CalPlug/Thrmostat_2_HVAC_IR_Controller/firmware/MQTT/AP.h

/**********************************
* CalPlug Portable AC Integration
* ESP32 Auto AP Script 
* 
* Navid Bazmoon
* Fall 2018
***********************************/

#ifndef _AP_
#define _AP_

#ifdef __cplusplus
extern "C" {
#endif


void APsetup();
void APloop();
void AProotPage();

#ifdef __cplusplus
}
#endif

#endif

/* EOF */
