CalPlug/Thrmostat_2_HVAC_IR_Controller/firmware/MQTT/ESP8266-Websocket/examples/WebSocketClientALT_Demo/WebSocketClientALT_Demo.ino

//Modified by Navid Bazmoon- University of California, Irvine.
//Included library modified from ESP8266WiFi.h to WiFi.h for compatibility with ESP32.

#include <ESP8266WiFi.h>
#include <WebSocketClient.h>

const char* ssid     = "SSID HERE";
const char* password = "PASSWORD HERE";
char path[] = "/";
char host[] = "echo.websocket.org";
  
WebSocketClient webSocketClient;

// Use WiFiClient class to create TCP connections
WiFiClient client;

void setup() {
  Serial.begin(115200);
  delay(10);

  // We start by connecting to a WiFi network

  Serial.println();
  Serial.println();
  Serial.print("Connecting to ");
  Serial.println(ssid);
  
  WiFi.begin(ssid, password);
  
  while (WiFi.status() != WL_CONNECTED) {
    delay(500);
    Serial.print(".");
  }

  Serial.println("");
  Serial.println("WiFi connected");  
  Serial.println("IP address: ");
  Serial.println(WiFi.localIP());

  delay(5000);
  

  // Connect to the websocket server
  if (client.connect("echo.websocket.org", 80)) {
    Serial.println("Connected");
  } else {
    Serial.println("Connection failed.");
    while(1) {
      // Hang on failure
    }
  }

  // Handshake with the server
  webSocketClient.path = path;
  webSocketClient.host = host;
  if (webSocketClient.handshake(client)) {
    Serial.println("Handshake successful");
  } else {
    Serial.println("Handshake failed.");
    while(1) {
      // Hang on failure
    }  
  }

}


void loop() {
  String data;

  if (client.connected()) {
    
    webSocketClient.getData(data);
    if (data.length() > 0) {
      Serial.print("Received data: ");
      Serial.println(data);
    }
    
    // capture the value of analog 1, send it along
    pinMode(1, INPUT);
    data = String(analogRead(1));
    
    webSocketClient.sendData(data);
    
  } else {
    Serial.println("Client disconnected.");
    while (1) {
      // Hang on disconnect.
    }
  }
  
  // wait to fully let the client disconnect
  delay(3000);
  
}
