CalPlug/Thrmostat_2_HVAC_IR_Controller/firmware/MQTT/EPROM_TEST.ino

/**********************************
* CalPlug Portable AC Integration
* ESP32 EEPROM Initializer
* 
* Navid Bazmoon
* Fall 2018
***********************************/


#include <EEPROM.h>
#include "EPROM.h"

#define NUM_ELEMENTS 10

char data2[150];

void save_data(char* data)

{
  Serial.println("Write data into EEPROM");
  EEPROM.begin(512);

  for (int i = 0; i < strlen(data); ++i)

  {
    EEPROM.write(i, (int)data[i]);
    delay(1);
  }
  EEPROM.commit();
  Serial.println("Write data complete");
  delay(1000);
}


void load_data(char* data)
{
  Serial.println("Read data from EEPROM");
  EEPROM.begin(512);
  int count = 0;
  int address = 0;
  while (count < NUM_ELEMENTS)
  {
    char read_char = (char)EEPROM.read(address);
    delay(1);
    strncat(data, &read_char, 1);
    if (read_char == '#')
      ++count;
    ++address;
  }

  Serial.println("Reading data is completed");
  Serial.println(data);
  delay(1000);

}



void wipe_data() 
{
  Serial.println("Wipe EEPROM");
  char* sep = "#";
  EEPROM.begin(512);
  for (int i = 0; i < NUM_ELEMENTS; ++i)

  {
    EEPROM.write(i, (int)sep);
    delay(1);
    EEPROM.write(i, 50);
    delay(1);
  }

  EEPROM.commit();
  Serial.println("Wipe data complete");
}


void EPROMsetup() {
  Serial.println();
  Serial.println();
  Serial.println("Welcome to the program");
  const char configured[] = "0";  
  const char ssid[] = "Default";
  const char pwd[] = "Default";
  const char mqtt_server[] = "m10.cloudmqtt.com";
  const char mqtt_port[] = "17934";
  const char mqtt_user[] = "dkpljrty";
  const char mqtt_pwd[] = "ZJDsxMVKRjoR";
  const char GFI[] = "800";
  const char level1[] = "270";
  const char level2[] = "270";

  wipe_data();
  char* sep = "#";
  char data[150] = {};
  strcat(data, configured);
  strcat(data, sep);
  strcat(data, ssid);
  strcat(data, sep);
  strcat(data, pwd);
  strcat(data, sep);
  strcat(data, mqtt_server);
  strcat(data, sep);
  strcat(data, mqtt_port);
  strcat(data, sep);
  strcat(data, mqtt_user);
  strcat(data, sep);
  strcat(data, mqtt_pwd);
  strcat(data, sep);
  strcat(data, GFI);
  strcat(data, sep);
  strcat(data, level1);
  strcat(data, sep);
  strcat(data, level2);
  strcat(data, sep);
  Serial.println("This is the final string:");
  Serial.println(data);
  Serial.println("The length is: ");
  Serial.println((unsigned)strlen(data));
  Serial.println();
  save_data(data);
  Serial.println("Second read:");
  load_data(data2);
  Serial.println(data2);
  Serial.println("Run Complete");
  delay (10000);
}
/*
void loop() {
  // No looped code in this sketch
  delay (1000); //restarting waiting loop
  Serial.println();
}
*/
